mackelec/Power_Scope/InverterScope_ILI9486/IS_120_references.ino

/*---------------------------------------------------------
 *  References for Libraries etc
-----------------------------------------------------------*/

//  http://docs.leaflabs.com/static.leaflabs.com/pub/leaflabs/maple-docs/0.0.12/lang/api/hardwaretimer.html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
//  http://docs.leaflabs.com/static.leaflabs.com/pub/leaflabs/maple-docs/0.0.12/timers.html
//  http://wiki.stm32duino.com/index.php?title=API#Pin_access
//  https://github.com/rogerclarkmelbourne/Arduino_STM32/tree/master/STM32F1/libraries/STM32ADC
//  https://github.com/rogerclarkmelbourne/Arduino_STM32/blob/master/STM32F1/cores/maple/HardwareTimer.cpp
//  https://learn.adafruit.com/adafruit-gfx-graphics-library/overview

/*---------------------------------------------------------
 *  Ideas for the Scope borrowed from these sources
-----------------------------------------------------------*/

//  http://stm32duino.com/viewtopic.php?f=19&t=107
//  https://github.com/pingumacpenguin/STM32-O-Scope

//  https://hackaday.io/project/20821-multiscope#menu-files
//  https://www.instructables.com/id/Fast-Portable-and-Affordable-Oscilloscope-and-Indu/


/*---------------------------------------------------------
 *  Related refs not not necessarily used
 ----------------------------------------------------------*/

//    http://www.mcufriend.com/main.html
//    https://github.com/prenticedavid/MCUFRIEND_kbv/tree/master/utility    (not using but good reference)
//    https://github.com/JoaoLopesF/SPFD5408     (not using - UNO library)


/*---------------------------------------------------------
 *  Other 
 ----------------------------------------------------------*/

//  http://arduiniana.org/libraries/streaming/
//  http://www.stm32duino.com/viewtopic.php?t=56    //  fast sqrt
//  http://www.barth-dev.de/online/rgb565-color-picker/
//  https://github.com/kosme/arduinoFFT/tree/master/Examples
